xxv/esphome-knob/housing/top.scad

use <housing.scad>

top();
