xxv/esphome-knob/housing/top_laser_cut_plate.scad

use <housing.scad>

top_laser_cut_plate();
